AndreasFMueller/GuiderPort/firmware/guiderport.c

/*
 * guiderport.c -- main function of the guiderport firmware
 *
 * (c) 2015 Prof Dr Andreas Müller, Hochschule Rapperswil
 */
#ifdef HAVE_CONFIG_H
#include <config.h>
#endif /* HAVE_CONFIG_H */
#include <port.h>
#include <timer.h>
#include <LUFA/Platform/Platform.h>
#include <LUFA/Drivers/USB/USB.h>
#include <avr/wdt.h>
#include <serial.h>

/**
 * \brief Main function for the guiderport firmware
 */
int	main(int argc, char *argv[]) {
	// show 
	for (int j = 0; j < 3; j++) {
		for (int i = 0; i < 4; i++) {
			port_value(i, 1);
			_delay_ms(100);
			port_value(i, 0);
		}
		port_value(2, 1);
		_delay_ms(100);
		port_value(2, 0);
		port_value(1, 1);
		_delay_ms(100);
		port_value(1, 0);
	}

	// initialize USB, but USB requests will only be hanled when 
	// interrupts are enabled below
	USB_Init(USB_DEVICE_OPT_FULLSPEED);

	// start the timer, this also enables the watchdog timer
	timer_start();

	// enable interrupts, let the show begin
	GlobalInterruptEnable();

	// do nothing
	for (;;) {
		USB_USBTask();
		if (newserial) {
			serial_write();
		}
	}
}


void wdt_init(void) __attribute__((naked)) __attribute__((section(".init3")));

/**
 * \brief enable the whatchdog timer 
 *
 * This method is called in the startup sequence
 */
void wdt_init(void) {
	MCUSR = 0;
	wdt_disable();
}
