AndreasFMueller/GuiderPort/firmware/event.c

/*
 * event.c -- enable event handling
 *
 * (c) 2015 Prof Dr Andreas Mueller, Hochschule Rapperswil
 */
#ifdef HAVE_CONFIG_H
#include <config.h>
#endif /* HAVE_CONFIG_H */
#include <event.h>
#include <port.h>
#include <LUFA/Drivers/USB/Core/Events.h>
#include <avr/wdt.h>
#include <serial.h>

/**
 * \brief RESET request
 *
 * The RESET request is handled by simply setting the whatdog timer to
 * such a short interval that it is bound to be triggered.
 */
void	process_reset() {
	Endpoint_ClearSETUP();
	Endpoint_ClearStatusStage();
	wdt_enable(WDTO_15MS);
}

/**
 * \brief SET request
 *
 * The SET request uses the value in wIndex as a bit mask to find out which
 * of the outputs should be affected by the request. It then uses the
 * contents of the wValue field to find the value that should be set on
 * the corresponding ports.
 */
void	process_set() {
	Endpoint_ClearSETUP();
	Endpoint_ClearStatusStage();
	for (unsigned char i = 0; i < 4; i++) {
		if (USB_ControlRequest.wIndex & (1 << i)) {
			port_value(i, USB_ControlRequest.wValue & (1 << i));
		}
	}
}

/**
 * \brief SET_PORT_TIME request
 *
 * The SET_PORT_TIME request sets the timer value for the port indicated
 * in the wIndex field of the request to the value specified in the wValue
 * field.
 */
void	process_set_port_time() {
	Endpoint_ClearSETUP();
	Endpoint_ClearStatusStage();
	port_set(USB_ControlRequest.wIndex & 0x3, USB_ControlRequest.wValue);
}

// buffer for the new timer values to be read from the control request
porttimes_t	newports;

/**
 * \brief SET_ALL_TIMES requests
 *
 * The SET_ALL_TIMES request reads 8 more bytes from the control requeest
 * and uses them as the timer values for all four ports.
 */
void	process_set_all_times() {
	Endpoint_ClearSETUP();
	Endpoint_Read_Control_Stream_LE((void *)newports, 8);
	Endpoint_ClearIN();
	port_set_all(newports);
}

/**
 * \brief SERIAL request
 *
 * read the new serial number in ascii from the USB and copy it into the
 * eeprom
 */
void    process_serial() {
	Endpoint_ClearSETUP();
	unsigned char	l = USB_ControlRequest.wLength;
	if (l <= 7) {
		Endpoint_Read_Control_Stream_LE(serialbuffer, l);
	}
	Endpoint_ClearIN();
	serialbuffer[l] = '\0';
	newserial = 1;
}

#define	is_control() \
	((USB_ControlRequest.bmRequestType & CONTROL_REQTYPE_TYPE) 	\
		== REQTYPE_VENDOR) 					\
	&&								\
	((USB_ControlRequest.bmRequestType & CONTROL_REQTYPE_RECIPIENT)\
		== REQREC_DEVICE)

#define	is_incoming() \
	((USB_ControlRequest.bmRequestType & CONTROL_REQTYPE_DIRECTION)	\
		== REQDIR_HOSTTODEVICE)

#define	is_outgoing() \
	((USB_ControlRequest.bmRequestType & CONTROL_REQTYPE_DIRECTION)	\
		== REQDIR_DEVICETOHOST)

/**
 * \brief Get the current LED state
 *
 * The GET request returns a single byte containing the state of all
 * the output ports.
 */
void	process_get() {
	Endpoint_ClearSETUP();
	unsigned char	v = port_get_all();
	Endpoint_Write_Control_Stream_LE((void *)&v, 1);
	Endpoint_ClearOUT();
}

/**
 * \brief Control request event handler
 *
 * This implementation handles the control requests for the GuiderPort device
 */
void	EVENT_USB_Device_ControlRequest() {
	if (is_control()) {
		if (is_incoming()) {
			switch (USB_ControlRequest.bRequest) {
			case GUIDERPORT_RESET:
				process_reset();
				break;
			case GUIDERPORT_SET:
				process_set();
				break;
			case GUIDERPORT_SET_PORT_TIME:
				process_set_port_time();
				break;
			case GUIDERPORT_SET_ALL_TIMES:
				process_set_all_times();
				break;
			case GUIDERPORT_SERIAL:
				process_serial();
				break;
			}
		}
		if (is_outgoing()) {
			switch (USB_ControlRequest.bRequest) {
			case GUIDERPORT_GET:
				process_get();
				break;
			}
		}
	}
}
