AndreasFMueller/GuiderPort/firmware/timer.h

/*
 * timer.h -- timer configuration
 *
 * (c) 2015 Prof Dr Andreas Mueller, Hochschule Rapperswil
 */
#ifndef _timer_h
#define _timer_h

extern void	timer_start();
extern void	timer_stop();

#endif /* _timer_h */
